JuanMen-2a/ohmetro-kelvin-esp32/Simulations/Sim1_Fuente_Corriente_TL431.asc

B1: voltage; {Vbat}
C1: cap; 100n
C2: cap; 10µ
Q2: npn; 2N2222A
R1: res; 1k
R2: res; 20k
R3: res; 5k
R4: res; 10
R_TEST: res; {Rt}
U1: TL431
U2: opamp2; LM358
Named nets: 0, VCC, VREF, VSET, v_base, v_volt
SIM 1 - Fuente de corriente constante TL431 + LM358 + 2N2222A (imagen 1)
I(R_TEST) = (2.495 V x R3/(R2+R3)) / R4 = 0.499 V / 10 ohm = 49.9 mA, independiente de R_TEST y de la bateria
.include modelos_miliohmimetro.lib
.options plotwinsize=0 numdgt=7
.param Vbat=3.7 Rt=1
.step param Vbat list 3.2 3.7 4.2
.step param Rt list 0.01 0.25 0.5 0.75 1
.tran 0 5m 0 5u
.meas TRAN I_test AVG I(R_TEST) FROM 4m TO 5m
.meas TRAN V_ref AVG V(VREF) FROM 4m TO 5m
.meas TRAN V_set AVG V(VSET) FROM 4m TO 5m
Graficar: I(R_TEST), V(VREF), V(VSET), V(v_volt)-V(v_base). Ver resultados .meas con View > SPICE Error Log (Ctrl+L).
B1 = bateria ICR18650-26J (3.2 a 4.2 V). R_TEST = resistencia bajo prueba (0.01 a 1 ohm).
