JuanMen-2a/ohmetro-kelvin-esp32/Simulations/Sim2_INA333.asc

C3: cap; 100n
D2: diode; 1N4148
D3: diode; 1N4148
I_FUENTE: current; 49.9m
R4: res; 10
R5: res; {RG}
R_TEST: res; {Rt}
U3: INA333
V1: voltage; 3.7
Named nets: VCC, 0, v_volt, v_base, V_AMP
SIM 2 - Amplificador de instrumentacion INA333 (imagen 2): G = 1 + 100k/R5
Entrada = caida en R_TEST con 49.9 mA (fuente de la SIM 1). Se comparan R5 = 2.5k (G=41, original) y R5 = 6.65k (G=16.04, corregido)
.include modelos_miliohmimetro.lib
.options plotwinsize=0 numdgt=7
.param Rt=0.5 RG=6.65k
.step param RG list 2.5k 6.65k
.step param Rt 0.001 1.201 0.02
.op
Despues de correr: graficar V(V_AMP) (eje X = Rt). Con R5=2.5k la salida se satura para Rt > ~0.48 ohm porque la
salida interna de A1 = V(v_base) - Vd*50k/R5 llega a 0 V (alimentacion simple, REF = 0). Con R5 = 6.65k es lineal hasta 1.2 ohm.
I_FUENTE es la fuente de corriente de la SIM 1 (equivalente ideal de 49.9 mA). D3 conduce ~0.16 mA a 0.5 V.
