JuanMen-2a/ohmetro-kelvin-esp32/Simulations/Sim3_ADS1252.asc

R27: res; 1k
U4: ADS1252; FCLK=1Meg
U5: XIAO_ESP32S3; FCLK=1Meg FSCLK=200k KOHM=2.495
V_AMP_SIM: voltage; PWL(0 0.1 0.8m 0.1 0.801m 0.4 1.6m 0.4 1.601m 0.8 2.4m 0.8 2.401m 1.6 3.2m 1.6 3.201m 2.4)
V_BAT: voltage; 3.7
V_REF: voltage; 2.495
Named nets: V_AMP, 0, V2V5, sclk, adc_out, clk, 3V3, D0, VCC, RMED, CODIGO
SIM 3 - ADC ADS1252 de 24 bits (imagen 3) leido por el XIAO ESP32-S3
Codigo = (V(VIN+) - V(VIN-)) / VREF x 2^23. CLK = 1 MHz -> 1 conversion cada 384 us. Pulso DRDY y 24 bits MSB primero por DOUT.
.include modelos_miliohmimetro.lib
.save V(clk) V(sclk) V(adc_out) V(V_AMP) V(CODIGO) V(RMED) V(3V3) V(V2V5)
.tran 0 4m 0 20n
(.save limita las senales guardadas para que el archivo .raw no sea enorme.) Graficar: V(clk), V(adc_out) (DOUT/DRDY), V(sclk) y V(CODIGO). Aqui KOHM = 2.495 -> V(RMED) = tension leida por el ADC.
V_REF = 2.495 V es la tension del TL431 (red 2.5V de la imagen). El ADS1252 real exige VDD = 4.75-5.25 V: el modelo no lo verifica.
