JuanMen-2a/ohmetro-kelvin-esp32/Simulations/Sim4_XIAO_ESP32S3.asc

B1: voltage; 3.7
LED5: LED; LED_YG
R26: res; 220
R27: res; 1k
U4: ADS1252; FCLK=1Meg
U5: XIAO_ESP32S3; FCLK=1Meg FSCLK=200k KOHM=3.1177
V_AMP_SIM: voltage; 0.8
V_REF: voltage; 2.495
Named nets: D0, clk, adc_out, sclk, 0, 3V3, VCC, RMED, CODIGO, V_AMP, V2V5
SIM 4 - XIAO ESP32-S3 (imagen 4): genera CLK y SCLK, lee los 24 bits y enciende el LED de actividad (D0)
LED5 + R26 = 220 ohm en D0: I_LED = (3.3 V - Vf) / 220 ohm. 3V3 sale del regulador interno alimentado por BAT+.
.include modelos_miliohmimetro.lib
.save V(D0) I(LED5) V(3V3) V(VCC) V(clk) V(sclk) V(adc_out) V(V_AMP) V(CODIGO) V(RMED)
.tran 0 2.5m 0 20n
Graficar: V(D0), I(LED5), V(3V3), V(sclk), V(adc_out), V(CODIGO) y V(RMED) (ohm; KOHM = 3.1177 ohm a escala completa).
V_AMP_SIM = 0.8 V equivale a R_TEST = 0.8/(16.04 x 49.9 mA) = 1.0 ohm con la ganancia corregida.
