JuanMen-2a/ohmetro-kelvin-esp32/Simulations/Sim5_Sistema_Completo.asc

B1: voltage; {Vbat}
C1: cap; 100n
C2: cap; 10µ
C3: cap; 100n
C4: cap; 100n
D2: diode; 1N4148
D3: diode; 1N4148
LED5: LED; LED_YG
Q2: npn; 2N2222A
R1: res; 1k
R2: res; 20k
R3: res; 5k
R4: res; 10
R5: res; 6.65k
R26: res; 220
R27: res; 1k
R_TEST: res; {Rt}
RL_I1: res; 0.05
RL_I2: res; 0.05
RL_S1: res; 0.05
RL_S2: res; 0.05
U1: TL431
U2: opamp2; LM358
U3: INA333
U4: ADS1252; FCLK=1Meg
U5: XIAO_ESP32S3; FCLK=1Meg FSCLK=200k KOHM=3.1177
Named nets: 0, VCC, VREF, VSET, I_N, I_P, DUT_A, DUT_B, v_volt, v_base, V_AMP, sclk, adc_out, clk, 3V3, D0, RMED, CODIGO
SIM 5 - SISTEMA COMPLETO: fuente de corriente -> R_TEST (Kelvin) -> INA333 -> ADS1252 -> XIAO ESP32-S3
Valores de la PCB: R4 = 10, R3 = 5k, R5 = 6.65k (G = 16.04). Cables Kelvin de 50 mohm cada uno. V(RMED) = resistencia medida (1 V = 1 ohm)
J2: conector Kelvin I+ S+ S- I- y cables de prueba (4 x 50 mohm)
.include modelos_miliohmimetro.lib
.param Vbat=3.7 Rt=1
.step param Rt list 0.005 0.05 0.25 0.5 1
.tran 0 2.5m 0 20n
.save V(VCC) V(VREF) V(VSET) V(V_AMP) V(v_volt) V(v_base) V(I_P) V(I_N) V(RMED) V(CODIGO) V(clk) V(sclk) V(adc_out) V(D0) V(3V3) I(R_TEST) I(R4) I(LED5)
.meas TRAN R_medida FIND V(RMED) AT=2.45m
.meas TRAN I_dut AVG I(R_TEST) FROM 2m TO 2.4m
R_medida (en el Error Log, Ctrl+L) debe coincidir con Rt. La entrada VREF (2.5V) del ADS1252 es la misma VREF del TL431.
