JuanMen-2a/ohmetro-kelvin-esp32/Simulations/Sim6_Elevador_MT3608_ADS1252.asc

B1: voltage; {Vbat}
C5: cap; 22µ; V=10 Rser=5m
C6: cap; 22µ; V=10 Rser=5m
C_F1: cap; 10µ; V=10 Rser=10m
C_F2: cap; 100n
D4: schottky; SS14
I_ADS: current; PWL(0 8m 3m 8m 3.001m 12m)
L1: ind; 4.7µ; Rser=50m
R1: res; 30.9k
R2: res; 10k
R_F: res; 10
U6: LT1935
Named nets: 0, VBAT, V5_BOOST, VDD_ADS
SIM 6 - Alimentacion de 5 V del ADS1252: elevador MT3608 (equivalente LT1935) + filtro capacitivo de VDD
MT3608 y LT1935: boost en modo corriente, 1.2 MHz, SOT-23. FB: MT3608 = 0.6 V (R1/R2 = 75k/10k), LT1935 = 1.255 V (30.9k/10k). Vout = 5.1 V
Filtro de VDD (hoja de datos TI ADS1252, 'Decoupling'): 1-10 uF en paralelo con 0.1 uF ceramico junto al pin; R_F = 10 ohm forma el filtro RC
.model SS14 D(Is=5u Rs=0.05 N=1.1 Cjo=100p BV=40 Ibv=1m)
.param Vbat=3.7
.step param Vbat list 3.3 3.7 4.2
.tran 0 4m 0 20n startup
.meas TRAN V_boost AVG V(V5_BOOST) FROM 2.5m TO 2.9m
.meas TRAN Rizado_boost PP V(V5_BOOST) FROM 2.5m TO 2.9m
.meas TRAN V_ads AVG V(VDD_ADS) FROM 2.5m TO 2.9m
.meas TRAN Rizado_ads PP V(VDD_ADS) FROM 2.5m TO 2.9m
.meas TRAN V_ads_12mA AVG V(VDD_ADS) FROM 3.6m TO 4m
I_ADS = consumo del ADS1252 (8 mA) y escalon a 12 mA a los 3 ms (buffer 74AHCT125 de CLK/SCLK). Ver resultados con Ctrl+L.
LTspice no tiene modelo del MT3608: se usa el LT1935 (misma topologia y frecuencia), como se hizo con LTC1734 en lugar del TP4056.
