JuanMen-2a/ohmetro-kelvin-esp32/Simulations/resultados/sim1_fuente_corriente.png

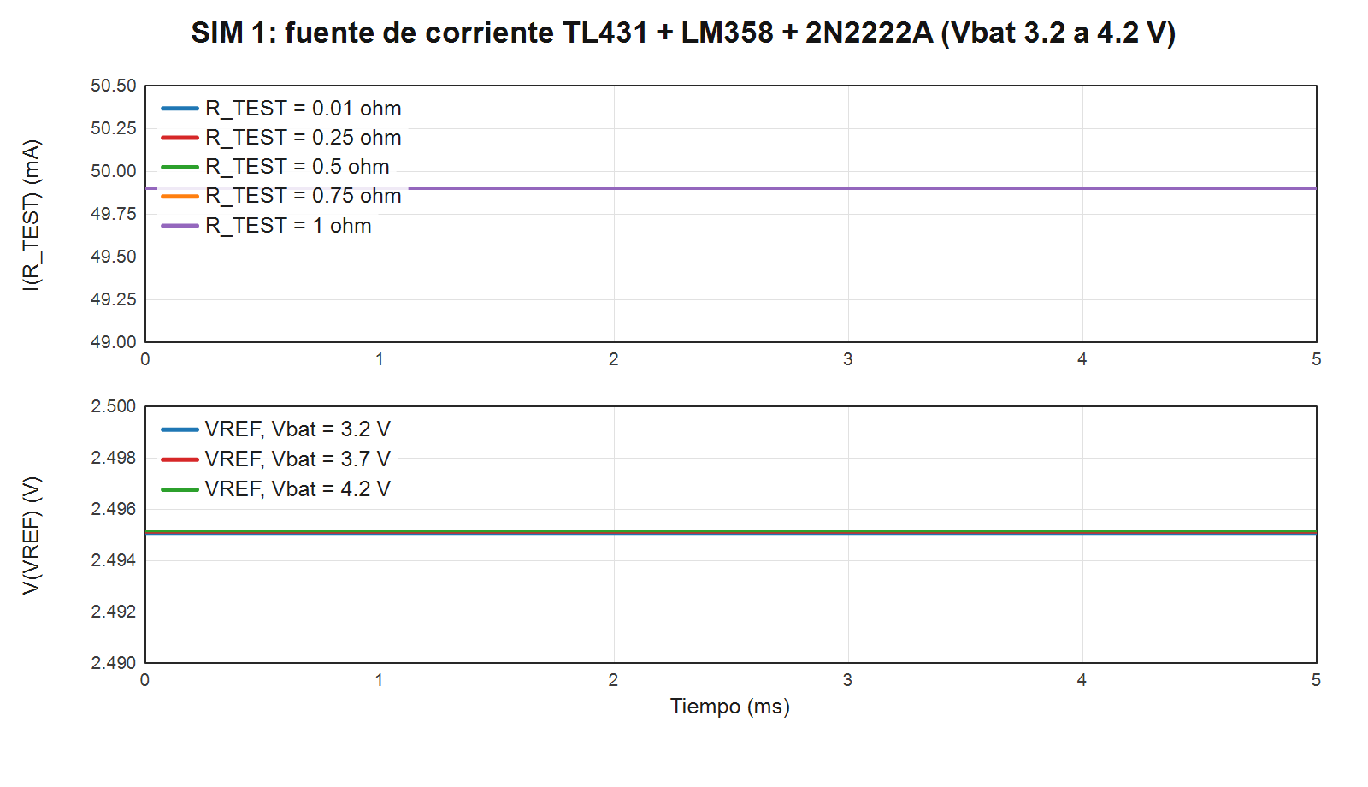
Simulations/resultados/sim1_fuente_corriente.png
