JuanMen-2a/ohmetro-kelvin-esp32/Simulations/resultados/sim2_ina333.png

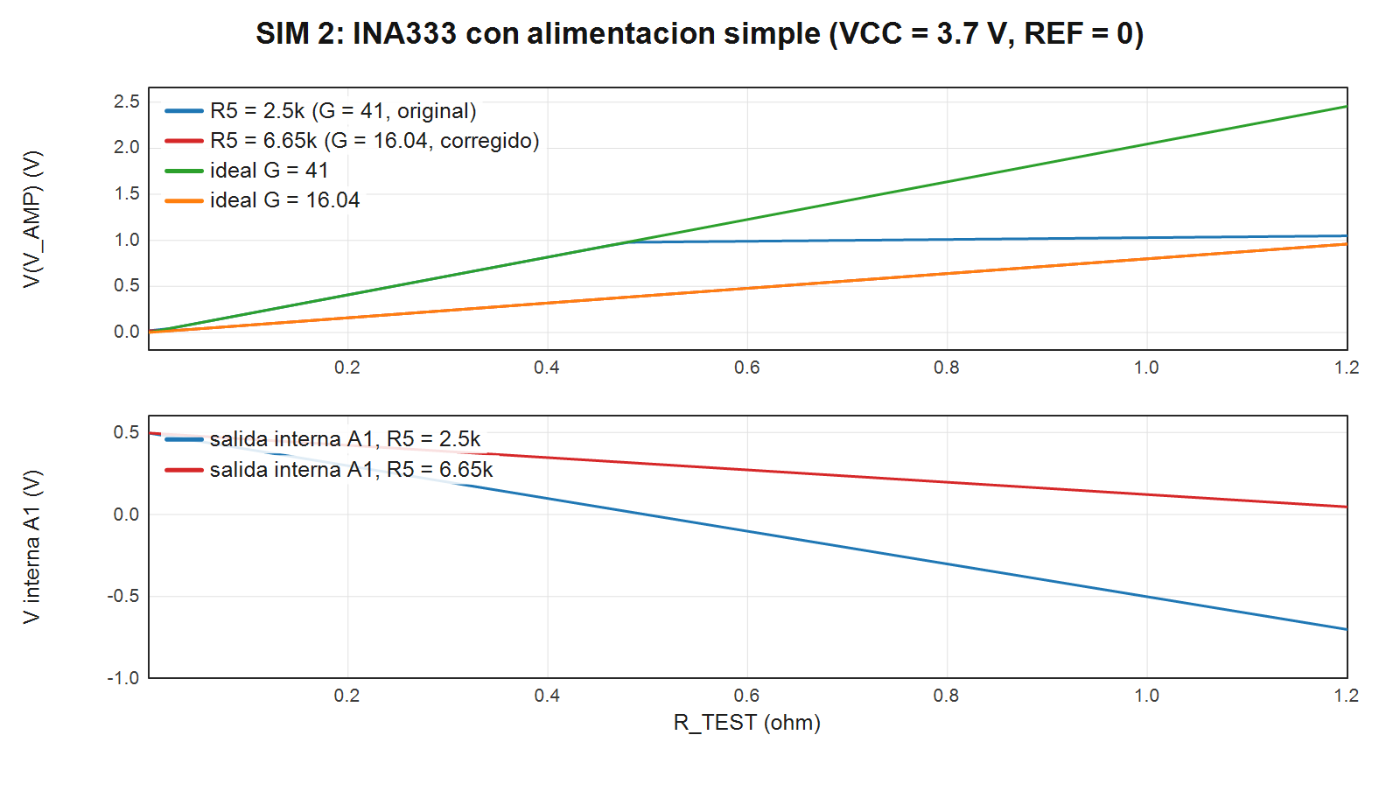
Simulations/resultados/sim2_ina333.png
