JuanMen-2a/ohmetro-kelvin-esp32/Simulations/resultados/sim3_ads1252.png

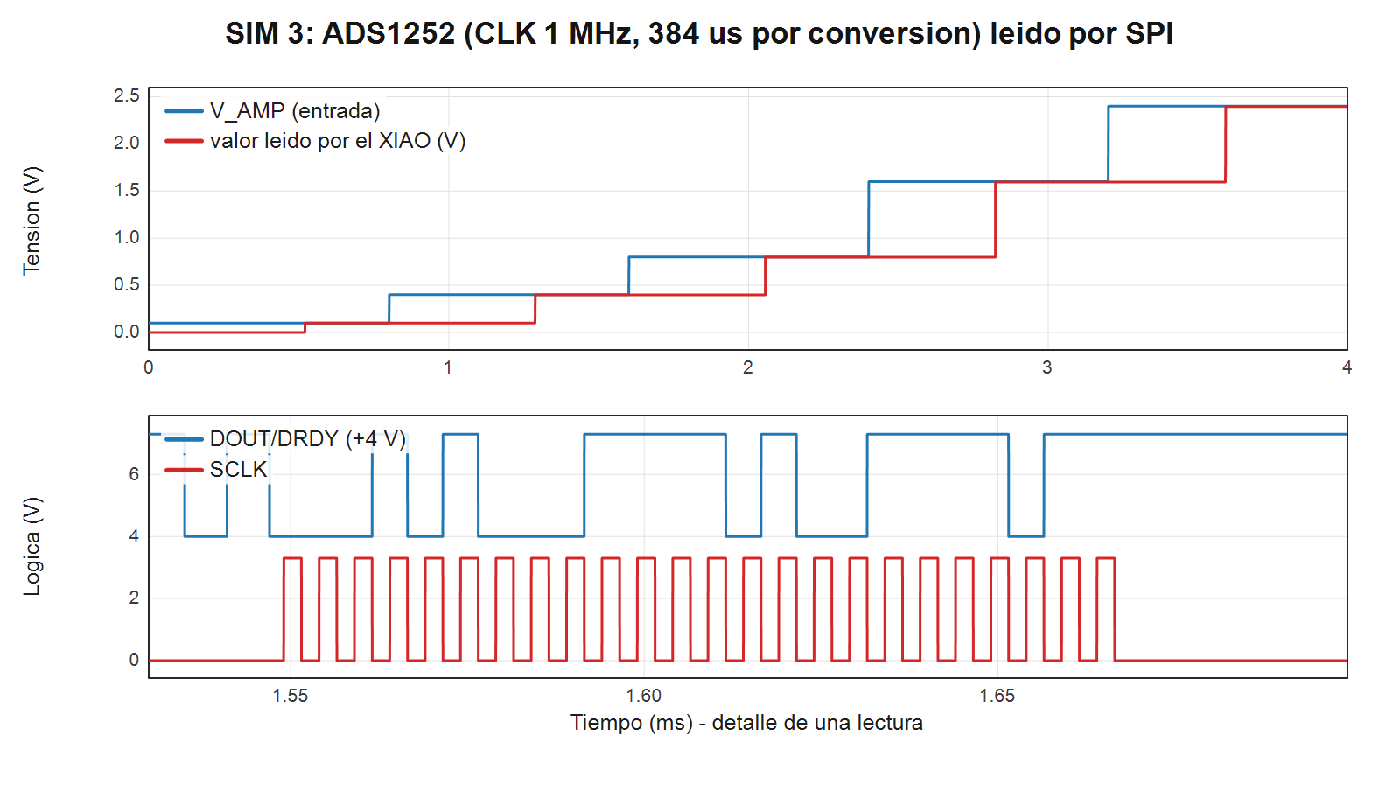
Simulations/resultados/sim3_ads1252.png
