JuanMen-2a/ohmetro-kelvin-esp32/Simulations/resultados/sim4_xiao.png

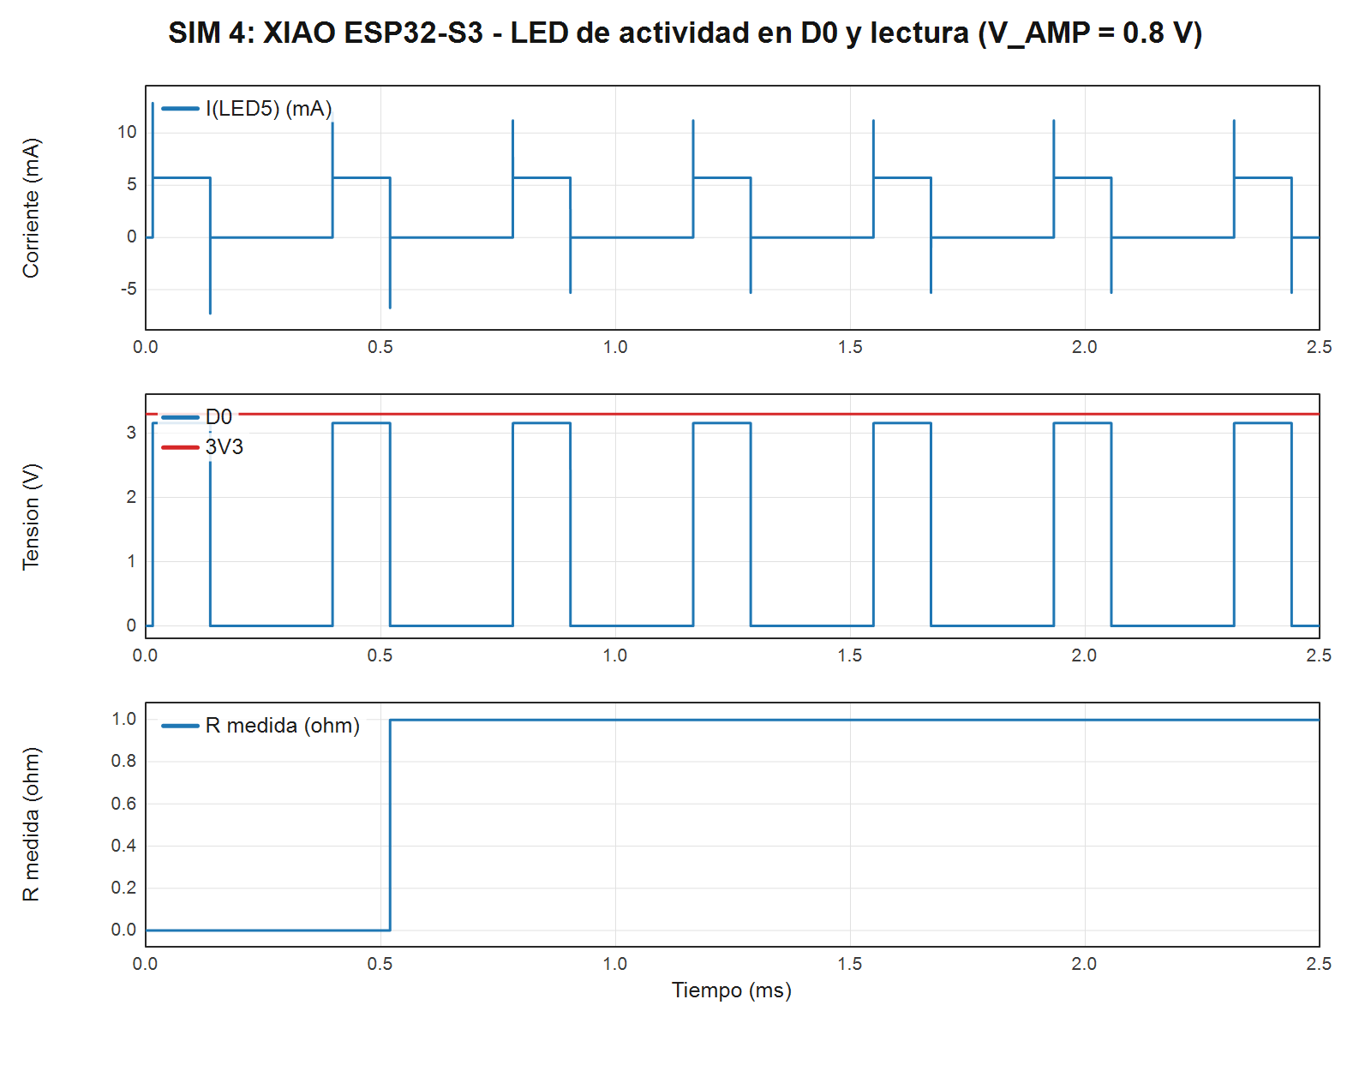
Simulations/resultados/sim4_xiao.png
