JuanMen-2a/ohmetro-kelvin-esp32/Simulations/resultados/sim5_sistema.png

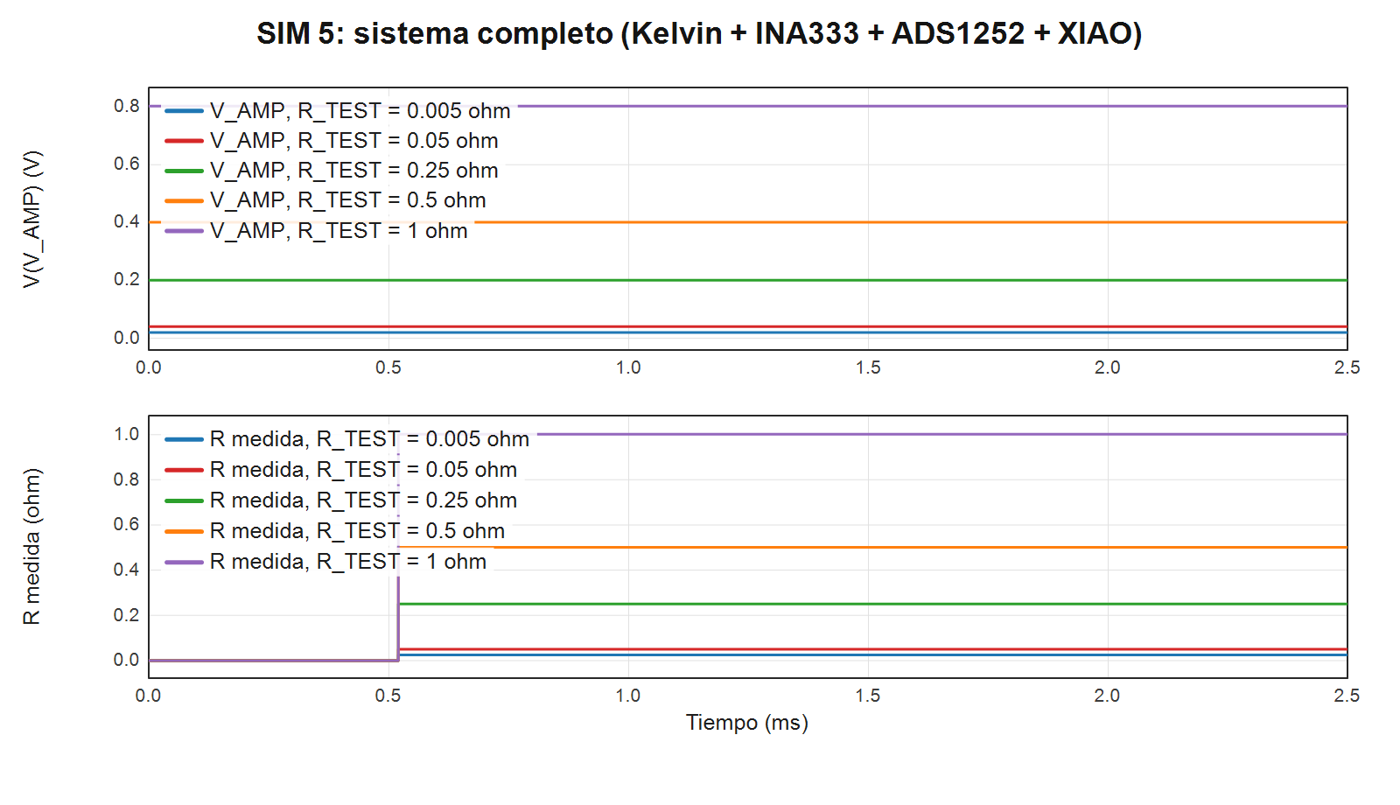
Simulations/resultados/sim5_sistema.png
