JuanMen-2a/ohmetro-kelvin-esp32/Simulations/resultados/sim6_mt3608_filtro.png

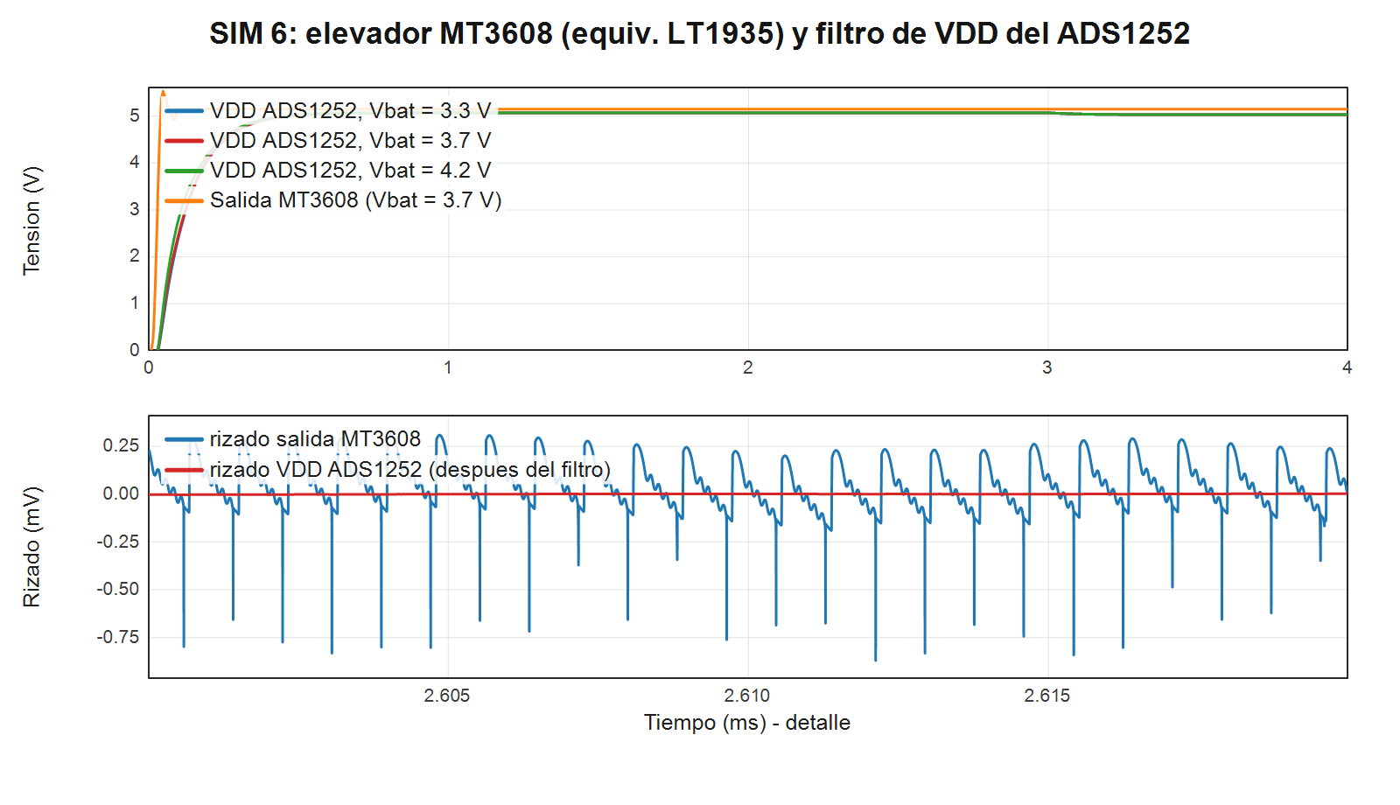
Simulations/resultados/sim6_mt3608_filtro.png
